kris92/Spirit_CBS/images/IMG_7888.jpeg

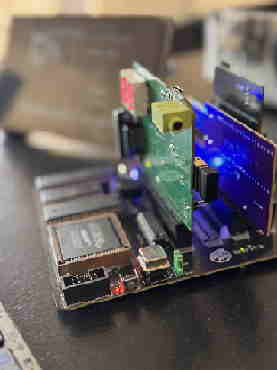
images/IMG_7888.jpeg
