kris92/Spirit_CBS/images/IMG_7889.jpeg

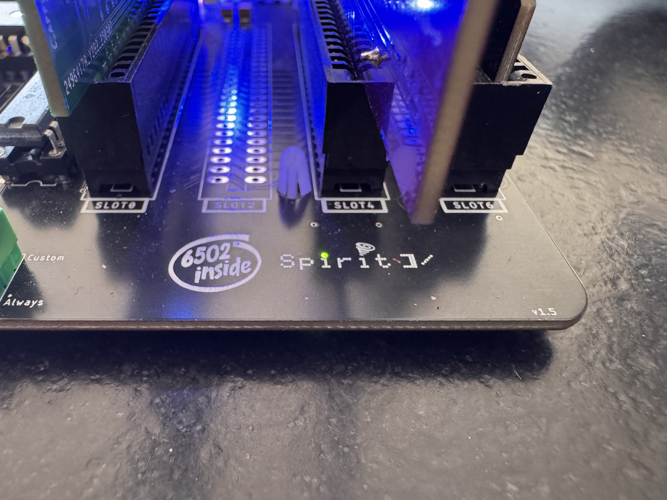
images/IMG_7889.jpeg
